delboy711/BST900-ESP32/images/IMG_20211011_142447.jpg

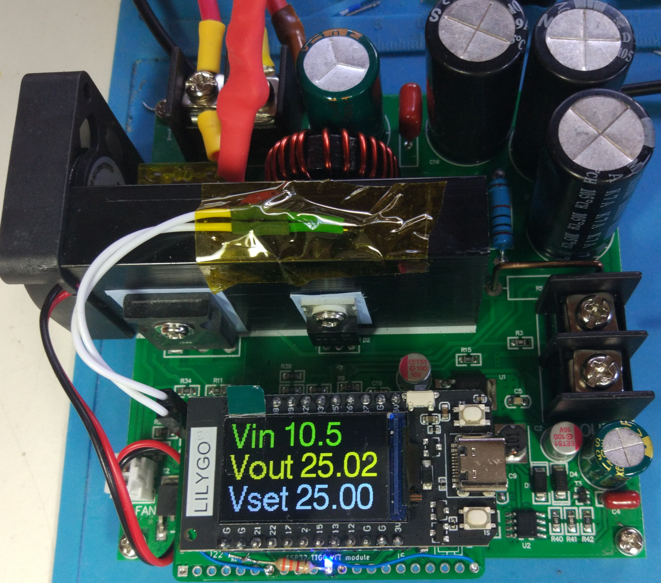
images/IMG_20211011_142447.jpg
