delboy711/BST900-ESP32/images/IMG_20211011_142528.jpg

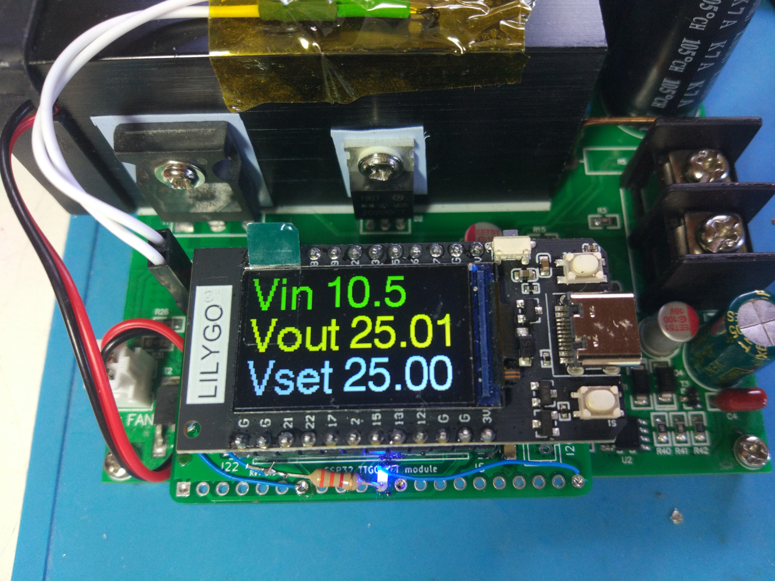
images/IMG_20211011_142528.jpg
