delboy711/BST900-ESP32/hardware/BST900-ESP32/BST900-ESP32.sch

## KiCad design hardware/BST900-ESP32/BST900-ESP32.sch (2021-11-02, an earlier design)

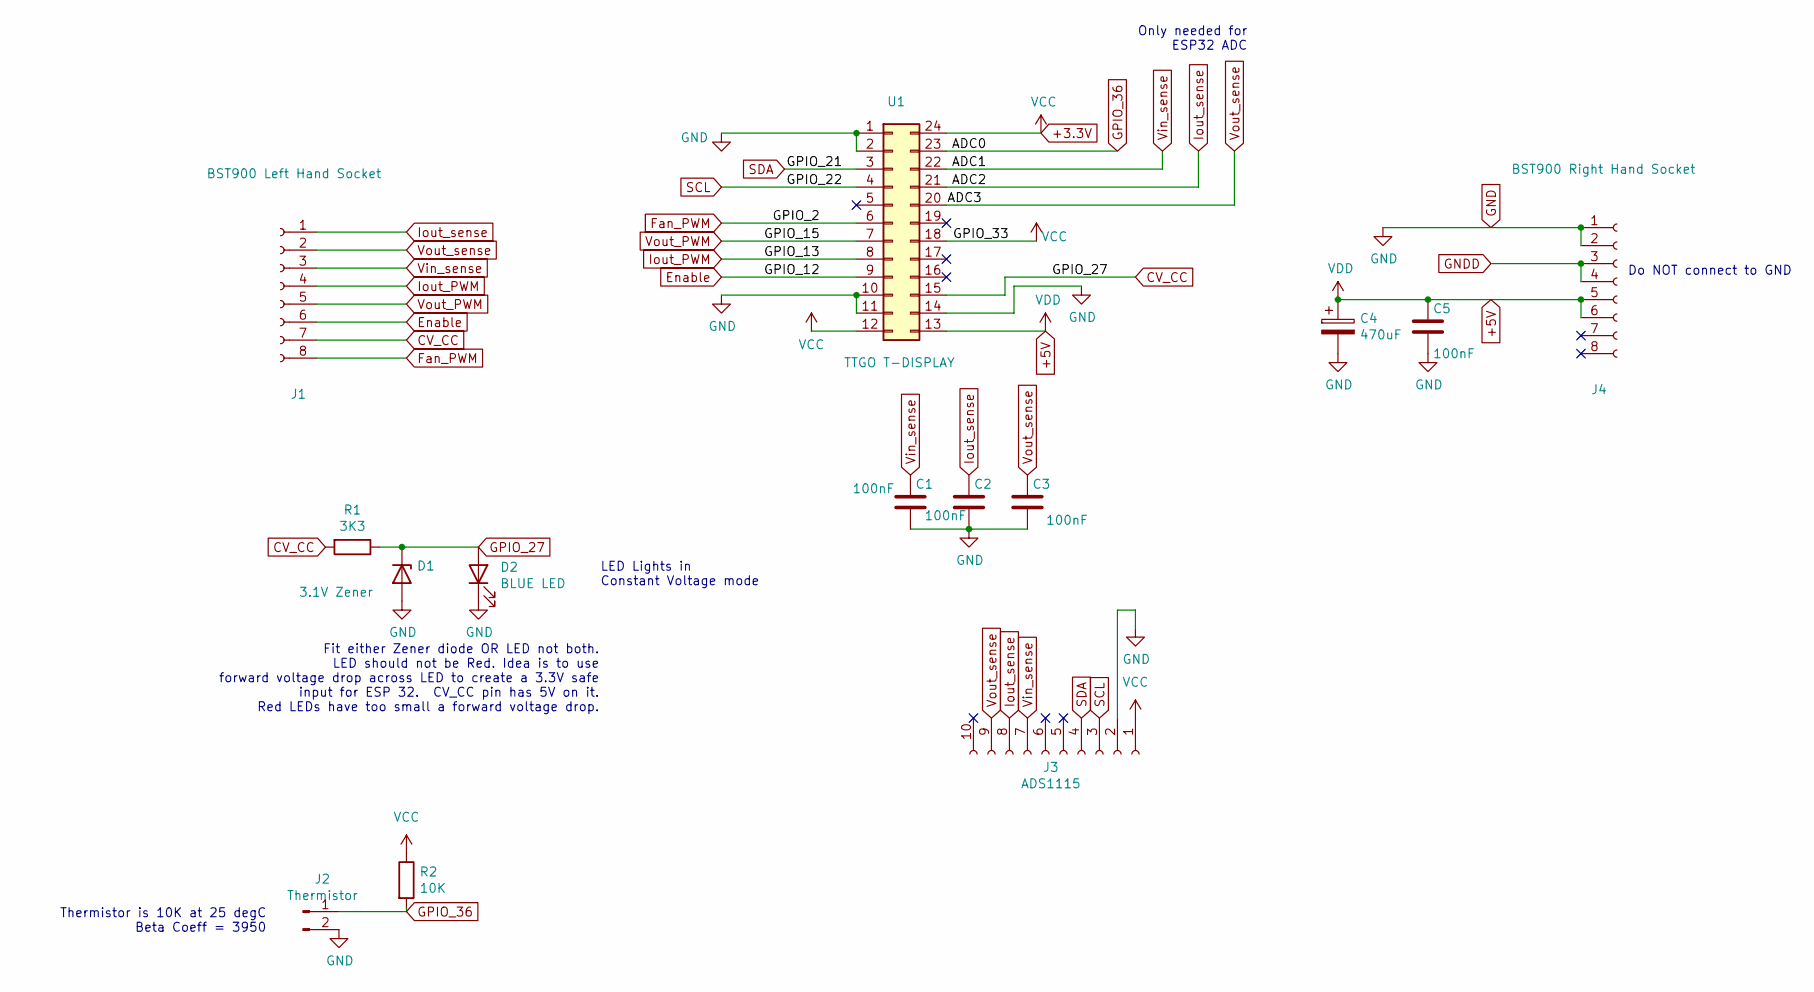
[picture p8: schematic BST900-ESP32.sch]

Parts:
C1, C2, C3, C5: 100nF
C4: 470uF
D1: 3.1V Zener
D2: BLUE LED
J1: BST900 Left Hand Socket
J2: Thermistor
J3: ADS1115
J4: BST900 Right Hand Socket
R1: 3K3
R2: 10K
U1: TTGO T-DISPLAY

Connections:
+3.3V: J3.1, R2.1, U1.12, U1.18, U1.24
+5V: C4.1, C5.1, J4.5, J4.6, U1.13
CV_CC: J1.7, R1.2, U1.15
Enable: J1.6, U1.9
Fan_PWM: J1.8, U1.6
GND: C1.2, C2.2, C3.2, C4.2, C5.2, D1.2 (A), D2.1 (K), J2.2, J3.2, J4.1, J4.2, U1.1, U1.2, U1.10, U1.11, U1.14
GNDD: J4.3, J4.4
GPIO_27: D1.1 (K), D2.2 (A), R1.1
GPIO_36: J2.1, R2.2, U1.23
Iout_PWM: J1.4, U1.8
Iout_sense: C2.1, J1.1, J3.8, U1.21
SCL: J3.3, U1.4
SDA: J3.4, U1.3
Vin_sense: C1.1, J1.3, J3.7, U1.22
Vout_PWM: J1.5, U1.7
Vout_sense: C3.1, J1.2, J3.9, U1.20

Notes on the sheet:
Do NOT connect to GND
Fit either Zener diode OR LED not both. LED should not be Red. Idea is to use forward voltage drop across LED to create a 3.3V safe input for ESP 32. CV_CC pin has 5V on it. Red LEDs have too small a forward voltage drop.
Thermistor is 10K at 25 degC Beta Coeff = 3950
Only needed for ESP32 ADC
LED Lights in Constant Voltage mode
