delboy711/BST900-ESP32/include/credentials.h

#define WIFI_SSID       "YOUR_SSID"
#define WIFI_PASSWORD   "YOUR_PASSWORD" 

#define MQTT_HOST "MQTT_SERVER_IP"
#define MQTT_USER "MQTT_USER"                //User name for your MQTT server
#define MQTT_PASSWORD "MQTT_PASSWORD"
#define MQTT_PORT 1883
